Fescron/universal-jlink-adapter/documentation/pictures/v4/pcb-front-v4.png

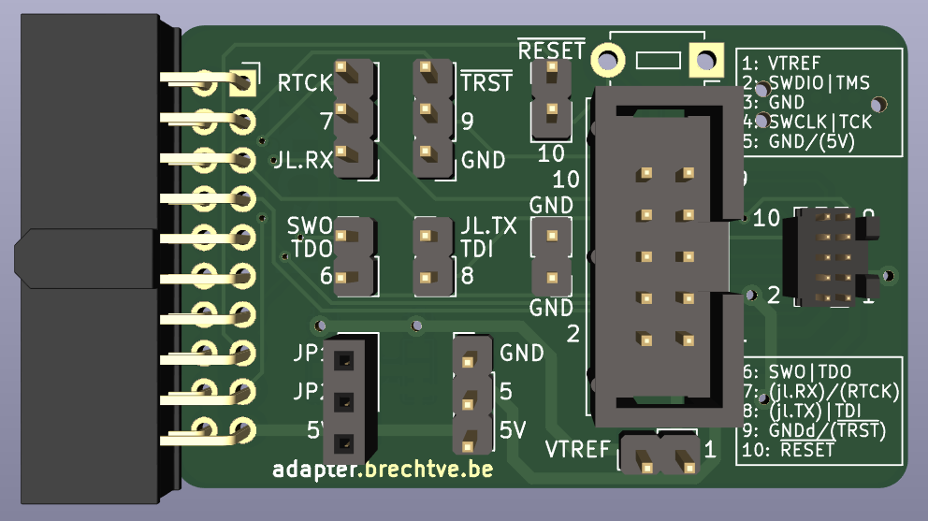
documentation/pictures/v4/pcb-front-v4.png
